tonberry-pico/tonberry-pico/software/src/utils/timer.py

# SPDX-License-Identifier: MIT
# Copyright (c) 2025 Matthias Blankertz <matthias@blankertz.org>

import asyncio
import heapq
import time
from utils import safe_callback

TIMER_DEBUG = True


class TimerManager(object):
    _instance = None

    def __new__(cls):
        if cls._instance is None:
            cls._instance = super(TimerManager, cls).__new__(cls)
            cls._instance.timers = []
            cls._instance.timer_debug = TIMER_DEBUG
            cls._instance.task = asyncio.create_task(cls._instance._timer_worker())
            cls._instance.worker_event = asyncio.Event()
        return cls._instance

    def schedule(self, when, what):
        cur_nearest = self.timers[0][0] if len(self.timers) > 0 else None
        self._remove_timer(what)  # Ensure timer is not already scheduled
        heapq.heappush(self.timers, (when, what))
        if cur_nearest is None or cur_nearest > self.timers[0][0]:
            # New timer is closer than previous closest timer
            if self.timer_debug:
                print(f'cur_nearest: {cur_nearest}, new next: {self.timers[0][0]}')
                print("schedule: wake")
            self.worker_event.set()

    def cancel(self, what):
        remove_idx = self._remove_timer(what)
        if remove_idx == 0:
            # Cancel timer was closest timer
            if self.timer_debug:
                print("cancel: wake")
            self.worker_event.set()
        return True

    def _remove_timer(self, what):
        try:
            (when, _), i = next(filter(lambda item: item[0][1] == what, zip(self.timers, range(len(self.timers)))))
        except StopIteration:
            return False
        del self.timers[i]
        heapq.heapify(self.timers)
        return i

    def _next_timeout(self):
        if len(self.timers) == 0:
            if self.timer_debug:
                print("timer: worker: queue empty")
            return None
        cur_nearest = self.timers[0][0]
        next_timeout = cur_nearest - time.ticks_ms()
        if self.timer_debug:
            if next_timeout > 0:
                print(f"timer: worker: next is {self.timers[0]}, sleep {next_timeout} ms")
            else:
                print(f"timer: worker: {self.timers[0]} elapsed @{cur_nearest}, delay {-next_timeout} ms")
        return next_timeout

    async def _wait(self, timeout):
        try:
            await asyncio.wait_for_ms(self.worker_event.wait(), timeout)
            if self.timer_debug:
                print("timer: worker: event")
            # got woken up due to event
            self.worker_event.clear()
            return True
        except asyncio.TimeoutError:
            return False

    async def _timer_worker(self):
        while True:
            next_timeout = self._next_timeout()
            if next_timeout is None or next_timeout > 0:
                await self._wait(next_timeout)
            else:
                _, callback = heapq.heappop(self.timers)
                safe_callback(callback, "timer callback")
